some-otter-thing/keepTheBoxGreen-arduino/Main/display_value.ino

void displayValue() {

  // topbar
  tft.setTextColor(ST7735_WHITE, ST7735_BLACK);                     // set text color to white and black background
  tft.setTextSize(1);                                               // set text size to 1
  tft.setCursor(85, 0);                                             // font starting coordinate of (x, y)
  tft.print(onlineStatus());

  // text block
  tft.setTextSize(1);
  tft.setCursor(0, 17);
  tft.setTextColor(ST7735_WHITE, ST7735_BLACK);
  if (WiFi.status() == WL_CONNECTED) {
    tft.print("WIFI ");
    tft.print(ssid);
  } else {
    tft.print("WIFI is disconnected ");
  }

  tft.setTextSize(1);

  // temp
  setTextColor(tempColor);
  tft.setCursor(0, 40);
  tft.print("Temperature: ");
  tft.print(temp);
  tft.print("C");

  // hum
  setTextColor(humColor);
  tft.setCursor(0, 55);
  tft.print("Humidity   : ");
  tft.print(hum);
  tft.print("%");

  // dust
  setTextColor(dustColor);
  tft.setCursor(0, 70);
  tft.print("Dust Level : ");
  PmResult pm = sds.readPm();
  // if (pm.isOk()) {
  //   tft.print(dust);
  // } else {
  //   tft.print("N/A    ");
  // }
  tft.print(dustMessage);

  // desk time
  setTextColor(sittingTimeColor);
  tft.setCursor(0, 85);
  tft.print("Desk Time  : ");
  // tft.print(timeSitting / 1000);
  tft.print(timeFormatting());

  // set notification in half below
  getNotification();
}

char* onlineStatus() {
  if (WiFi.status() == WL_CONNECTED) {
    return "Online";
  } else {
    return "Offline";
  }
}
