some-otter-thing/keepTheBoxGreen-arduino/Main/connect_mqtt.ino

void connectMQTT()
{
  Serial.print("Attempting to MQTT broker: ");
  Serial.print(broker);
  Serial.println(" ");

  while (!mqttClient.connect(broker, 8883) && mqttRetries < MAX_MQTT_RETRIES)
  {
    Serial.print(".");
    Serial.println(mqttClient.connectError());
    mqttRetries ++;
    delay(2000);
  }
  // subscribe to a topic
  mqttClient.subscribe("devices/" + deviceId + "/messages/devicebound/#");
}
