some-otter-thing/keepTheBoxGreen-arduino/Main/publish_message.ino

void publishMessage()
{
  Serial.println("Publishing message");
  const int capacity = JSON_ARRAY_SIZE(10) + 10*JSON_OBJECT_SIZE(2)+ JSON_OBJECT_SIZE(3) + 280;     // TODO: calculation of the JSON doc size should be redone
  StaticJsonDocument<capacity> doc;
  serializeJson(doc, Serial);
  doc["connectionDeviceId"] = "keep-the-box-green-device";
  doc["connectionDeviceGenerationId"] = "637669621042053570";
  doc["temperature"] = temp;
  doc["humidity"] = hum;
  doc["dustConcentration"] = 64.8; // TODO: add real one
  doc["sittingTime"] = timeSitting;

  // TODO: can be removed, it serializes the document in the serial monitor
  serializeJson(doc, Serial);
  Serial.println(" ");

  char payload[1024];
  size_t payloadSize = serializeJson(doc, payload);

  mqttClient.beginMessage("devices/" + deviceId + "/messages/events/", static_cast<unsigned long>(payloadSize));
  mqttClient.print(payload);
  mqttClient.endMessage();
}
